radioelf/DronPi/images/IMG_20161122_113929.jpg

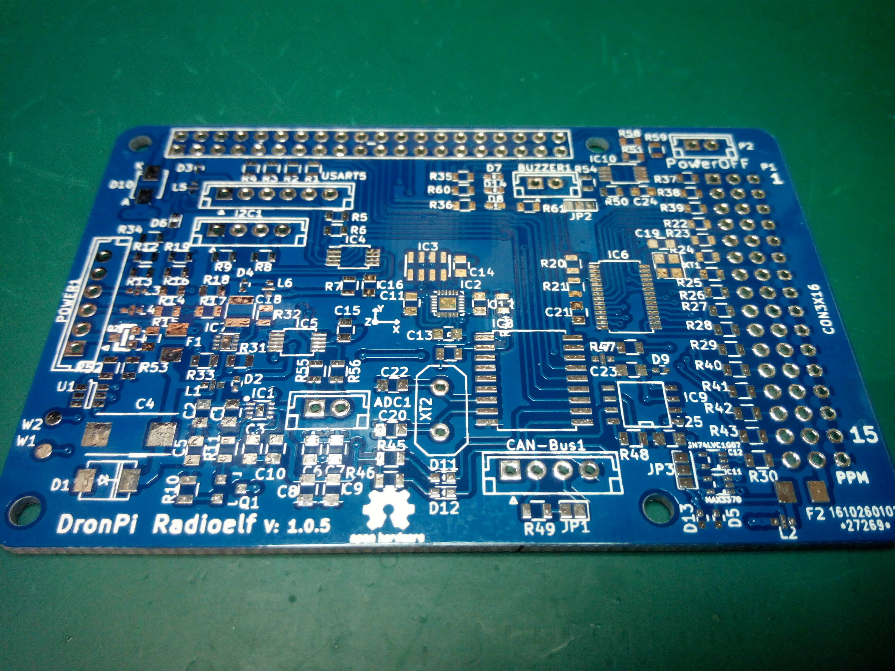
images/IMG_20161122_113929.jpg
